LaskaKit/ESPink-42/SW/ESPink_4_2_APDS9960/OpenSansSB_32px.h

// Created by http://oleddisplay.squix.ch/ Consider a donation
// In case of problems make sure that you are using the font file with the correct version!
const uint8_t Open_Sans_SemiBold_32Bitmaps[] PROGMEM = {

	// Bitmap Data:
	0x00, // ' '
	0xFB,0xEF,0xBC,0x71,0xC7,0x1C,0x71,0xC7,0x1C,0x71,0xC7,0x1C,0x00,0x07,0x3E,0xFB,0xE7,0x00, // '!'
	0xF3,0xDE,0x7B,0xCF,0x70,0xEE,0x1C,0xC3,0x18,0x63,0x0C, // '"'
	0x01,0xC3,0x00,0x18,0x70,0x03,0x87,0x00,0x38,0x70,0x03,0x87,0x00,0x38,0x60,0x03,0x86,0x07,0xFF,0xFE,0x7F,0xFF,0xE7,0xFF,0xFE,0x07,0x0E,0x00,0x70,0xC0,0x06,0x1C,0x00,0xE1,0xC0,0xFF,0xFF,0xCF,0xFF,0xFC,0xFF,0xFF,0xC0,0xC3,0x80,0x1C,0x38,0x01,0xC3,0x80,0x1C,0x38,0x01,0xC7,0x00,0x18,0x70,0x00, // '#'
	0x03,0x00,0x06,0x00,0x0C,0x00,0x7F,0x03,0xFF,0xCF,0xFF,0x3E,0xC6,0x79,0x80,0xF3,0x01,0xE6,0x03,0xEC,0x03,0xF8,0x03,0xF8,0x03,0xFC,0x01,0xFE,0x01,0xFE,0x03,0x3C,0x06,0x38,0x0C,0x70,0x19,0xEE,0x37,0xDF,0xFF,0x3F,0xFC,0x1F,0xE0,0x03,0x00,0x06,0x00,0x0C,0x00, // '$'
	0x1F,0x00,0x38,0x07,0xF0,0x0E,0x01,0xFF,0x01,0xC0,0x38,0xE0,0x70,0x07,0x1C,0x1C,0x01,0xC3,0x83,0x80,0x38,0x38,0xE0,0x07,0x07,0x1C,0x00,0xE1,0xC7,0x00,0x0E,0x38,0xE7,0xC1,0xC7,0x39,0xFC,0x3F,0xEF,0x7F,0xC3,0xF9,0xCE,0x38,0x3E,0x71,0xC7,0x00,0x0E,0x78,0x70,0x03,0x8E,0x0E,0x00,0x71,0xC1,0xC0,0x1C,0x1C,0x38,0x03,0x83,0x8E,0x00,0xE0,0x71,0xC0,0x38,0x0F,0xF8,0x07,0x00,0xFE,0x01,0xC0,0x0F,0x80, // '%'
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
	  {  1401,  14,  23,  19,    3,  -23 }, // 'E'
	  {  1442,  14,  23,  18,    3,  -23 }, // 'F'
	  {  1483,  20,  23,  24,    2,  -23 }, // 'G'
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
};
const GFXfont OpenSansSB_32px PROGMEM = {
(uint8_t  *)Open_Sans_SemiBold_32Bitmaps,(GFXglyph *)Open_Sans_SemiBold_32Glyphs,0x20, 0x7E, 45};
