LaskaKit/ESPink-42/SW/Weatherstation_info/OpenSansSB_24px.h

// Created by http://oleddisplay.squix.ch/ Consider a donation
// In case of problems make sure that you are using the font file with the correct version!
const uint8_t Open_Sans_SemiBold_24Bitmaps[] PROGMEM = {

	// Bitmap Data:
	0x00, // ' '
	0xEE,0xEE,0xEE,0xEE,0xEE,0xEC,0x0E,0xEE,0xE0, // '!'
	0x66,0x33,0x19,0x8C,0xC6,0x63,0x30, // '"'
	0x06,0x30,0x0C,0x60,0x18,0xC0,0x71,0x80,0xC6,0x0F,0xFF,0x9F,0xFF,0x06,0x30,0x18,0xE0,0x31,0x83,0xFF,0xF7,0xFF,0xE3,0x8C,0x06,0x38,0x0C,0x60,0x18,0xC0,0x31,0x80, // '#'
	0x06,0x00,0x30,0x07,0xF0,0xFF,0xC7,0x66,0x73,0x03,0x98,0x0E,0xC0,0x7E,0x00,0xFC,0x01,0xF8,0x0D,0xC0,0x67,0x03,0x3B,0x1B,0x9F,0xFC,0x7F,0x80,0x30,0x01,0x80, // '$'
	0x3C,0x06,0x07,0xE0,0xE0,0xE6,0x0C,0x0C,0x71,0x80,0xC7,0x18,0x0C,0x73,0x00,0xC7,0x70,0x0E,0x66,0x78,0x7E,0xEF,0xC3,0xCC,0xCE,0x01,0xDC,0x60,0x19,0xC6,0x03,0x1C,0x60,0x71,0xC6,0x06,0x0C,0xE0,0xE0,0xFC,0x0C,0x07,0x80, // '%'
	0x0F,0x80,0x0F,0xF0,0x03,0x8E,0x00,0xC3,0x80,0x30,0xE0,0x0E,0x70,0x01,0xFC,0x00,0x3C,0x00,0x3F,0x07,0x1F,0xE1,0xCF,0x3C,0xE3,0x83,0xB8,0xE0,0x7C,0x38,0x0F,0x07,0x0F,0xC1,0xFF,0xB8,0x1F,0x87,0x00, // '&'
	0xDB,0x6D,0x80, // '''
	0x1C,0x30,0xE3,0x87,0x0C,0x38,0x70,0xE1,0xC3,0x87,0x0E,0x1C,0x38,0x30,0x70,0xE0,0xE0,0xC1,0xC0, // '('
	0xE0,0xC1,0xC1,0x83,0x83,0x06,0x0E,0x1C,0x38,0x70,0xE1,0xC3,0x87,0x0C,0x38,0x71,0xC3,0x0E,0x00, // ')'
	0x0E,0x00,0xE0,0x0E,0x08,0x42,0xFF,0xEF,0xFE,0x0E,0x01,0xB0,0x3B,0x83,0x18,0x11,0x00, // '*'
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
	  {   817,  11,  17,  14,    2,  -17 }, // 'E'
	  {   841,  11,  17,  14,    2,  -17 }, // 'F'
	  {   865,  15,  17,  18,    1,  -17 }, // 'G'
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
};
const GFXfont OpenSansSB_24px PROGMEM = {
(uint8_t  *)Open_Sans_SemiBold_24Bitmaps,(GFXglyph *)Open_Sans_SemiBold_24Glyphs,0x20, 0x7E, 33};
