LaskaKit/ESPink-42/SW/Weatherstation_info/OpenSansSB_50px.h

// Created by http://oleddisplay.squix.ch/ Consider a donation
// In case of problems make sure that you are using the font file with the correct version!
const uint8_t Open_Sans_SemiBold_50Bitmaps[] PROGMEM = {

	// Bitmap Data:
	0x00, // ' '
	0x7E,0x3F,0x1F,0x8F,0xC7,0xE3,0xF1,0xF8,0xFC,0x7E,0x3F,0x1F,0x8F,0xC7,0xE3,0xF1,0xF8,0xFC,0x7E,0x3E,0x0F,0x07,0x83,0xC1,0xE0,0xF0,0x78,0x3C,0x00,0x00,0x00,0x00,0x00,0x00,0xF0,0xFC,0xFE,0x7F,0xBF,0x8F,0xC3,0xC0, // '!'
	0xFC,0x3F,0x7E,0x1F,0xBF,0x0F,0xCF,0x87,0xC7,0xC3,0xE3,0xE1,0xF1,0xE0,0x78,0xF0,0x3C,0x78,0x1E,0x3C,0x0F,0x1E,0x07,0x8F,0x03,0xC7,0x81,0xE0, // '"'
	0x00,0x1E,0x07,0xC0,0x00,0x3C,0x0F,0x00,0x00,0xF8,0x1E,0x00,0x01,0xF0,0x3C,0x00,0x03,0xC0,0x78,0x00,0x07,0x81,0xF0,0x00,0x0F,0x03,0xC0,0x00,0x3E,0x07,0x80,0x00,0x7C,0x0F,0x00,0x00,0xF8,0x1E,0x00,0xFF,0xFF,0xFF,0xF1,0xFF,0xFF,0xFF,0xE3,0xFF,0xFF,0xFF,0xC7,0xFF,0xFF,0xFF,0x80,0x3E,0x07,0x80,0x00,0x78,0x1F,0x00,0x00,0xF0,0x3E,0x00,0x01,0xE0,0x78,0x00,0x03,0xC0,0xF0,0x00,0x0F,0x81,0xE0,0x00,0x1F,0x03,0xC0,0x00,0x3C,0x0F,0x80,0x3F,0xFF,0xFF,0xFC,0x7F,0xFF,0xFF,0xF8,0xFF,0xFF,0xFF,0xF1,0xFF,0xFF,0xFF,0xE0,0x0F,0x03,0xE0,0x00,0x1E,0x07,0xC0,0x00,0x3C,0x0F,0x00,0x00,0x78,0x1E,0x00,0x01,0xF0,0x3C,0x00,0x03,0xC0,0xF8,0x00,0x07,0x81,0xF0,0x00,0x0F,0x03,0xC0,0x00,0x1E,0x07,0x80,0x00,0x7C,0x0F,0x00,0x00, // '#'
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
};
const GFXglyph Open_Sans_SemiBold_50Glyphs[] PROGMEM = {
// bitmapOffset, width, height, xAdvance, xOffset, yOffset
	  {     0,   1,   1,  14,    0,    0 }, // ' '
	  {     1,   9,  37,  15,    3,  -36 }, // '!'
	  {    43,  17,  13,  23,    3,  -36 }, // '"'
	  {    71,  31,  36,  33,    1,  -36 }, // '#'
	  {   211,  24,  41,  30,    3,  -38 }, // '$'
	  {   334,  40,  36,  44,    2,  -36 }, // '%'
	  {   514,  36,  36,  38,    2,  -36 }, // '&'
	  {   676,   7,  13,  13,    3,  -36 }, // '''
	  {   688,  14,  44,  17,    2,  -36 }, // '('
	  {   765,  13,  44,  17,    2,  -36 }, // ')'
	  {   837,  24,  23,  28,    2,  -38 }, // '*'
	  {   906,  26,  24,  30,    2,  -30 }, // '+'
	  {   984,   9,  12,  14,    2,   -6 }, // ','
	  {   998,  13,   5,  17,    2,  -16 }, // '-'
	  {  1007,   9,   7,  15,    3,   -6 }, // '.'
	  {  1015,  21,  36,  21,    0,  -36 }, // '/'
	  {  1110,  26,  36,  30,    2,  -36 }, // '0'
	  {  1227,  16,  36,  30,    4,  -36 }, // '1'
	  {  1299,  26,  36,  30,    2,  -36 }, // '2'
	  {  1416,  26,  36,  30,    2,  -36 }, // '3'
	  {  1533,  28,  36,  30,    1,  -36 }, // '4'
	  {  1659,  24,  36,  30,    3,  -36 }, // '5'
	  {  1767,  26,  36,  30,    2,  -36 }, // '6'
	  {  1884,  26,  36,  30,    2,  -36 }, // '7'
	  {  2001,  26,  36,  30,    2,  -36 }, // '8'
	  {  2118,  26,  36,  30,    2,  -36 }, // '9'
	  {  2235,   9,  29,  15,    3,  -28 }, // ':'
	  {  2268,   9,  34,  15,    2,  -28 }, // ';'
	  {  2307,  26,  25,  30,    2,  -31 }, // '<'
	  {  2389,  24,  14,  30,    3,  -25 }, // '='
	  {  2431,  26,  25,  30,    2,  -31 }, // '>'
	  {  2513,  23,  37,  24,    0,  -36 }, // '?'
	  {  2620,  40,  40,  46,    3,  -36 }, // '@'
	  {  2820,  34,  36,  34,    0,  -36 }, // 'A'
	  {  2973,  26,  36,  34,    5,  -36 }, // 'B'
	  {  3090,  28,  36,  33,    3,  -36 }, // 'C'
	  {  3216,  30,  36,  38,    5,  -36 }, // 'D'
	  {  3351,  21,  36,  29,    5,  -36 }, // 'E'
	  {  3446,  21,  36,  28,    5,  -36 }, // 'F'
	  {  3541,  30,  36,  37,    3,  -36 }, // 'G'
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
};
const GFXfont OpenSansSB_50px PROGMEM = {
(uint8_t  *)Open_Sans_SemiBold_50Bitmaps,(GFXglyph *)Open_Sans_SemiBold_50Glyphs,0x20, 0x7E, 69};
