LaskaKit/ESPink-42/SW/Simple/display_test/OpenSansSB_40px.h

// Created by http://oleddisplay.squix.ch/ Consider a donation
// In case of problems make sure that you are using the font file with the correct version!
const uint8_t Open_Sans_SemiBold_40Bitmaps[] PROGMEM = {

	// Bitmap Data:
	0x00, // ' '
	0xFB,0xEF,0xBE,0xFB,0xEF,0xBE,0xFB,0xEF,0xBE,0xF9,0xE7,0x9C,0x71,0xC7,0x1C,0x00,0x00,0x1C,0xFB,0xEF,0xBE,0x70, // '!'
	0xF1,0xEF,0x1E,0xF1,0xEF,0x1E,0xF1,0xEF,0x1E,0xF1,0xEE,0x0E,0xE0,0xEE,0x0E, // '"'
	0x00,0x70,0x78,0x00,0x78,0x38,0x00,0x3C,0x1C,0x00,0x1E,0x0E,0x00,0x0E,0x0F,0x00,0x07,0x07,0x80,0x07,0x83,0x80,0x03,0xC1,0xC0,0x7F,0xFF,0xFF,0x3F,0xFF,0xFF,0x9F,0xFF,0xFF,0xC0,0x38,0x38,0x00,0x3C,0x1C,0x00,0x1E,0x0E,0x00,0x0E,0x0F,0x00,0x07,0x07,0x80,0x03,0x83,0x80,0x7F,0xFF,0xFF,0x3F,0xFF,0xFF,0x9F,0xFF,0xFF,0xC0,0x70,0x78,0x00,0x38,0x38,0x00,0x3C,0x1C,0x00,0x1E,0x0E,0x00,0x0F,0x0F,0x00,0x07,0x07,0x80,0x03,0x83,0xC0,0x01,0xC1,0xC0,0x01,0xE0,0xE0,0x00, // '#'
	0x00,0xE0,0x00,0x0E,0x00,0x00,0xE0,0x00,0x3F,0xE0,0x1F,0xFF,0xC3,0xFF,0xFC,0x7F,0xFF,0xC7,0xEE,0x38,0xF8,0xE0,0x0F,0x8E,0x00,0xF8,0xE0,0x07,0xCE,0x00,0x7F,0xE0,0x03,0xFE,0x00,0x1F,0xF8,0x00,0xFF,0xE0,0x03,0xFF,0x80,0x0F,0xFC,0x00,0xEF,0xC0,0x0E,0x3E,0x00,0xE3,0xE0,0x0E,0x3E,0x80,0xE3,0xEF,0x0E,0xFC,0xFF,0xFF,0xCF,0xFF,0xF8,0xFF,0xFF,0x01,0xFF,0x80,0x00,0xE0,0x00,0x0E,0x00,0x00,0xE0,0x00,0x0E,0x00, // '$'
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
	  {  1597,  18,  29,  19,    0,  -29 }, // '?'
	  {  1663,  33,  32,  37,    2,  -29 }, // '@'
	  {  1795,  27,  29,  27,    0,  -29 }, // 'A'
	  {  1893,  21,  29,  27,    4,  -29 }, // 'B'
	  {  1970,  23,  29,  26,    2,  -29 }, // 'C'
	  {  2054,  24,  29,  30,    4,  -29 }, // 'D'
	  {  2141,  17,  29,  23,    4,  -29 }, // 'E'
	  {  2203,  17,  29,  22,    4,  -29 }, // 'F'
	  {  2265,  25,  29,  30,    2,  -29 }, // 'G'
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
};
const GFXfont OpenSansSB_40px PROGMEM = {
(uint8_t  *)Open_Sans_SemiBold_40Bitmaps,(GFXglyph *)Open_Sans_SemiBold_40Glyphs,0x20, 0x7E, 55};
